wilco2009/zx80-81-Double-Clone/Labels/Keyboards.png

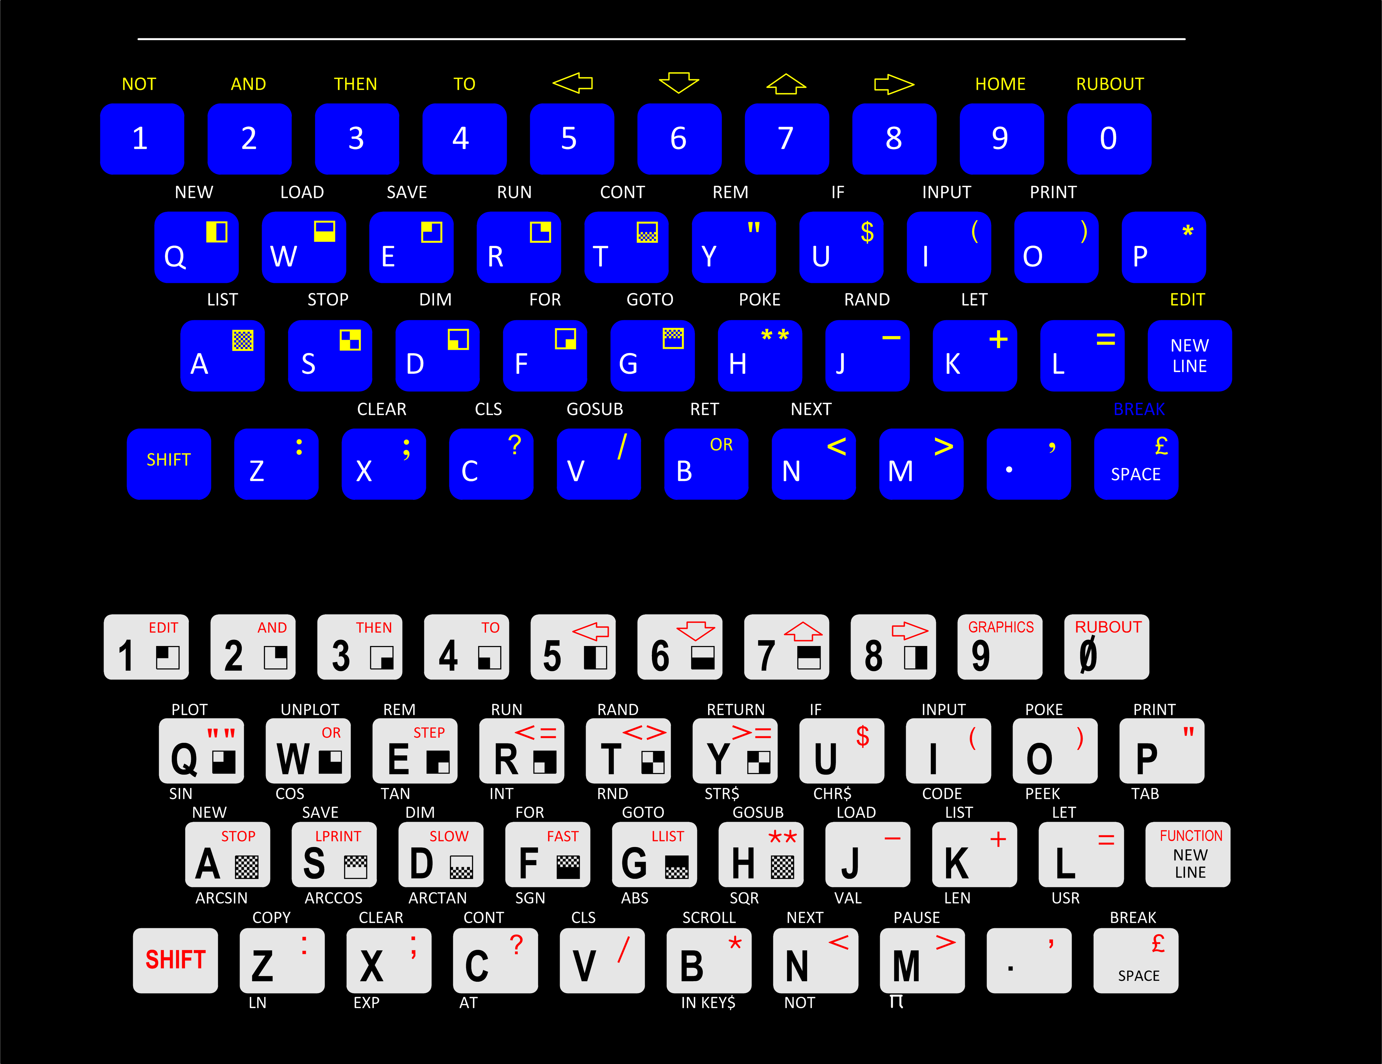
Labels/Keyboards.png
