wilco2009/zx80-81-Double-Clone/Labels/zx80 RAYAS.png

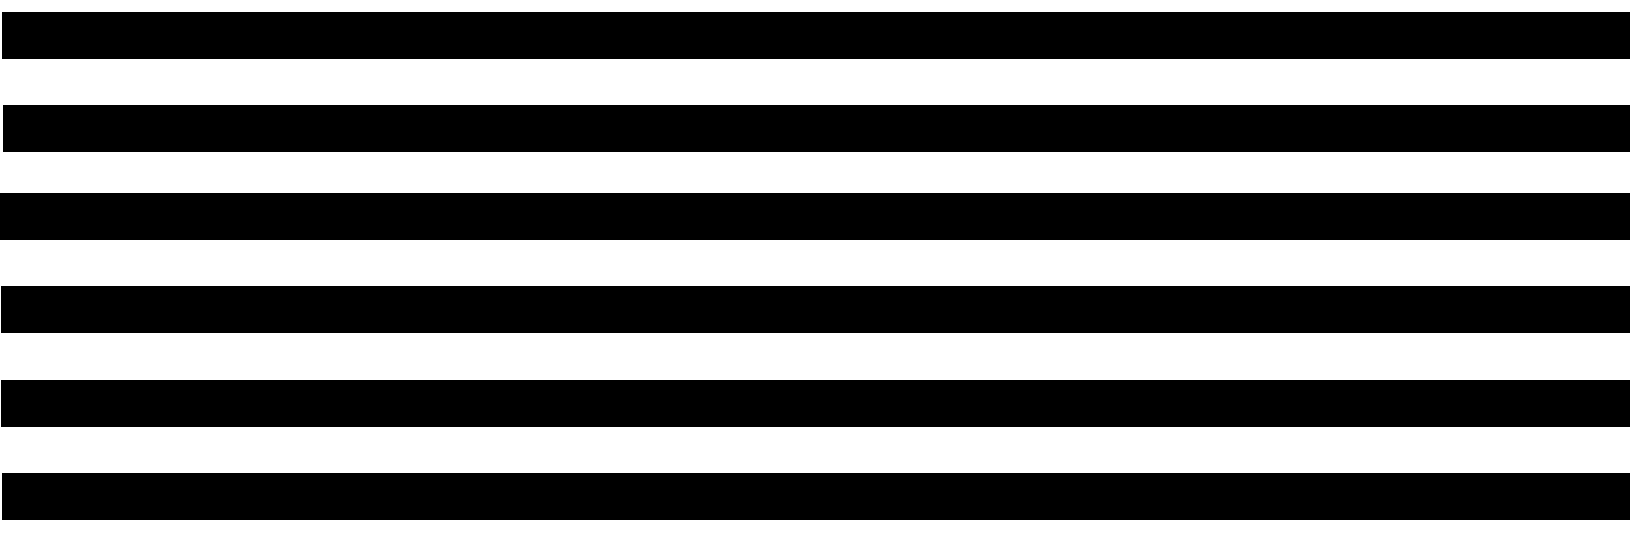
Labels/zx80 RAYAS.png
