wilco2009/zx80-81-Double-Clone/doc/esquema_zx80_build034_amplizx81.png

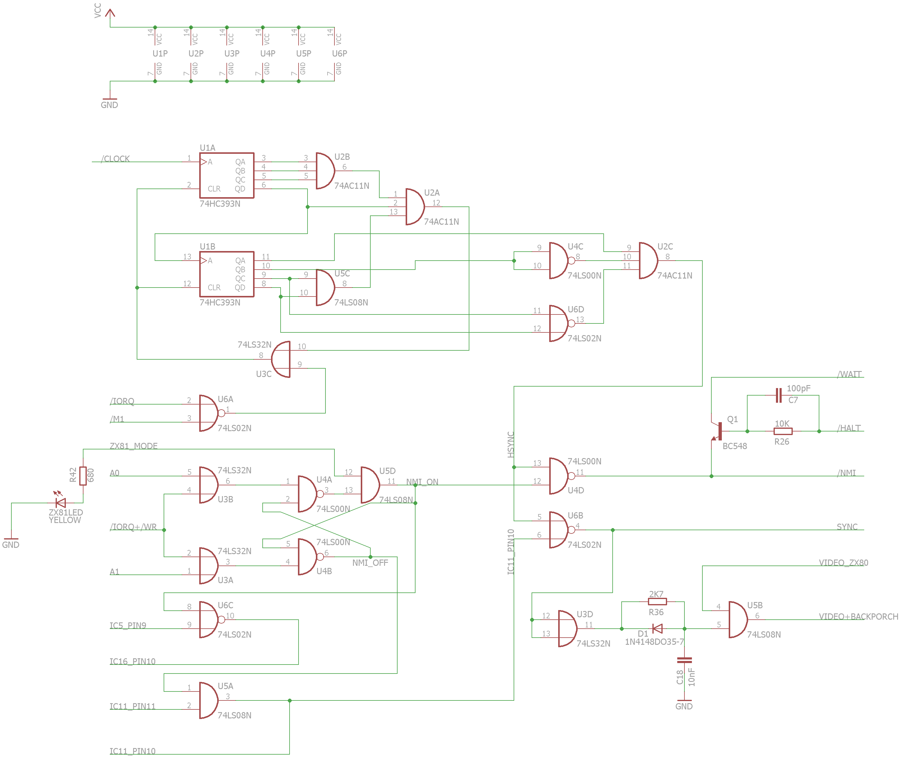
doc/esquema_zx80_build034_amplizx81.png
