wilco2009/zx80-81-Double-Clone/doc/esquema_zx80_build034_lm.png

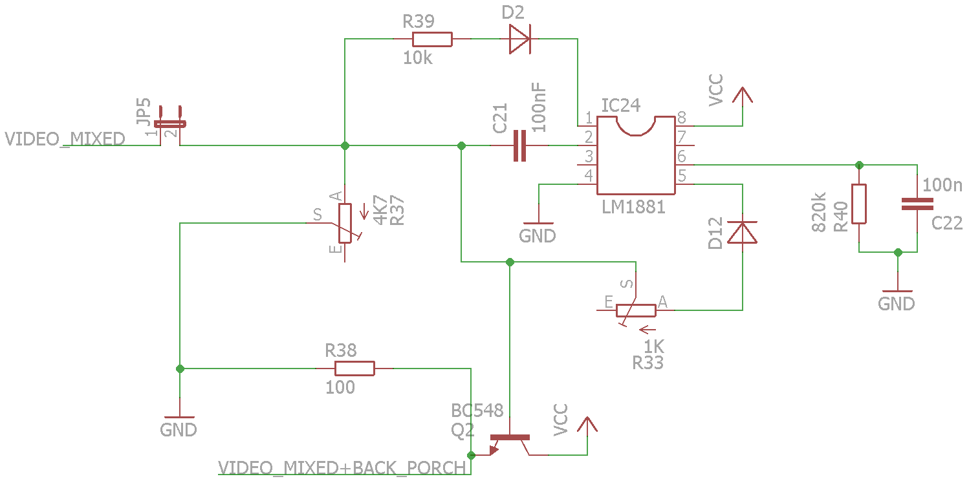
doc/esquema_zx80_build034_lm.png
