wilco2009/zx80-81-Double-Clone/doc/esquema_zx80_build034_principal.png

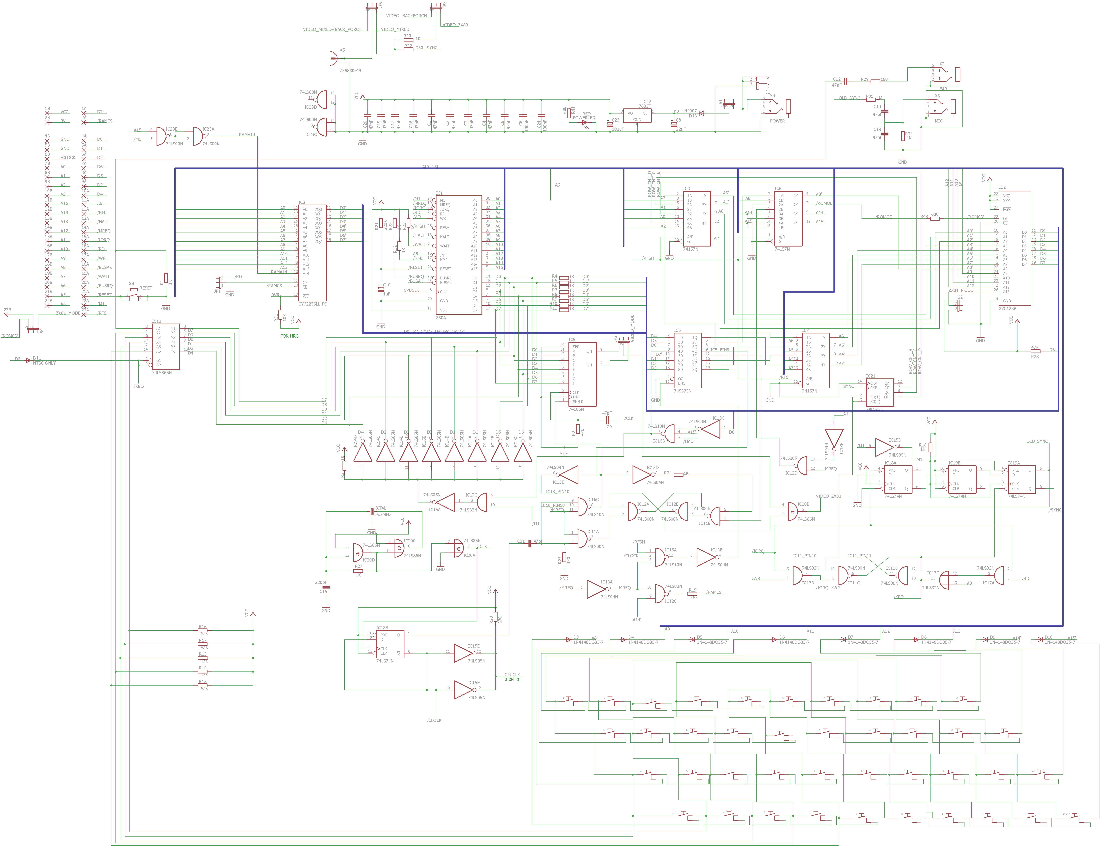
doc/esquema_zx80_build034_principal.png
