wilco2009/zx80-81-Double-Clone/Labels/todo.png

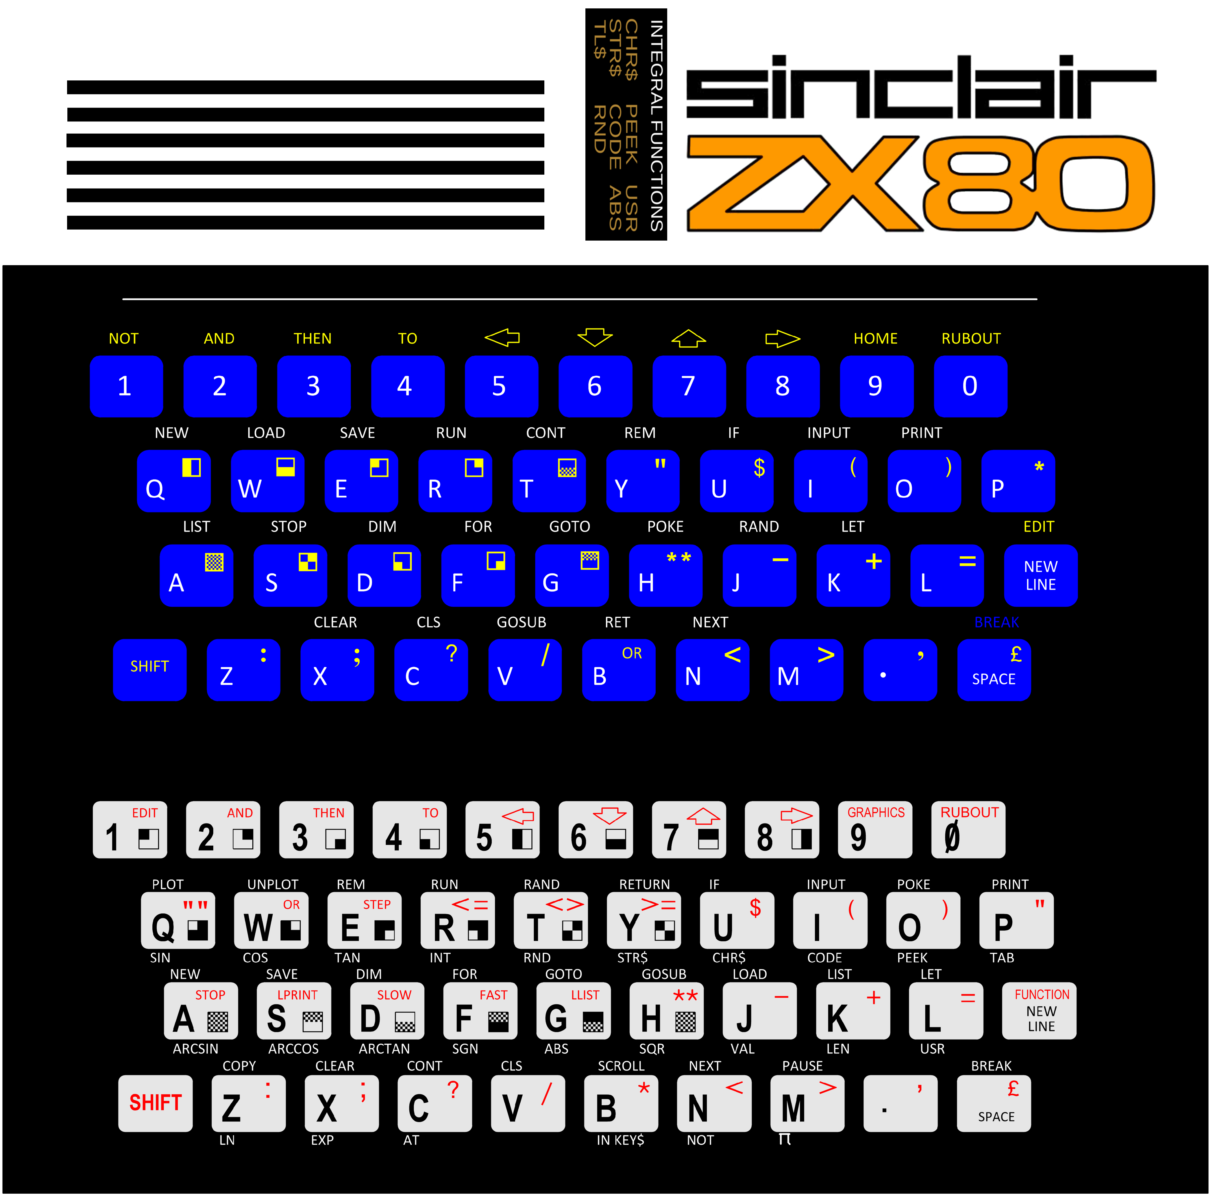
Labels/todo.png
